Alby312/BalancerRobot_Mk1/Electronics/BalancerRobot_Mk1.kicad_sch

## KiCad design Electronics/BalancerRobot_Mk1.kicad_sch (2025-12-15)

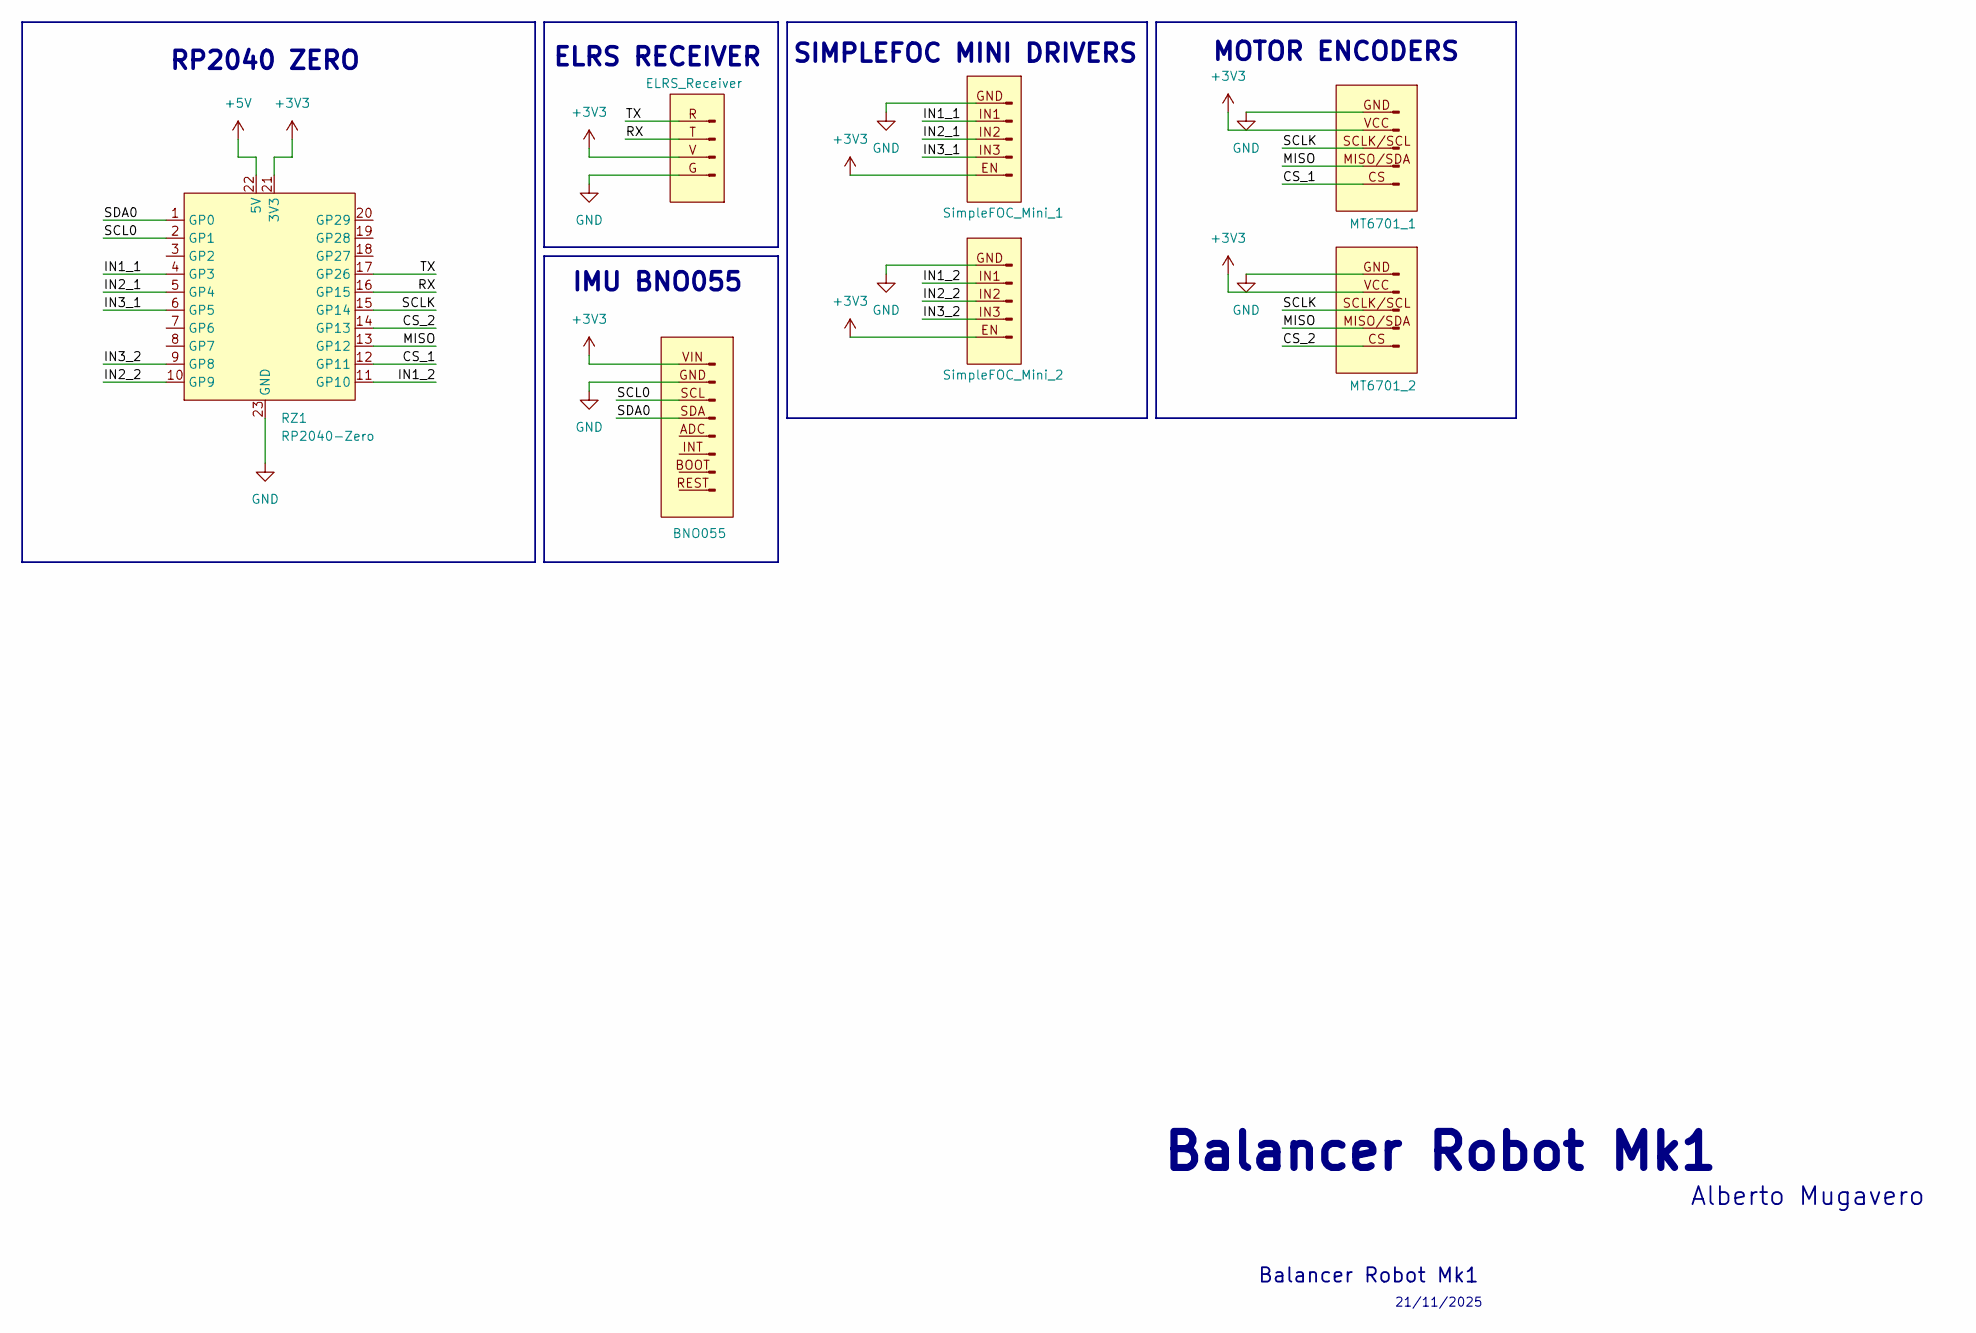
[picture p6: schematic BalancerRobot_Mk1.kicad_sch]

Parts:
BNO055: Conn_01x04_Pin
ELRS_Receiver: Conn_01x04_Pin
MT6701_1, MT6701_2: Conn_01x04_Pin
RZ1: RP2040-Zero
SimpleFOC_Mini_1, SimpleFOC_Mini_2: Conn_01x04_Pin

Connections:
+3V3: BNO055.VIN (Pin_1), ELRS_Receiver.V (Pin_2), MT6701_1.VCC (Pin_2), MT6701_2.VCC (Pin_2), RZ1.21 (3V3), SimpleFOC_Mini_1.EN (Pin_5), SimpleFOC_Mini_2.EN (Pin_5)
+5V: RZ1.22 (5V)
CS_1: MT6701_1.CS (Pin_5), RZ1.12 (GP11)
CS_2: MT6701_2.CS (Pin_5), RZ1.14 (GP13)
GND: BNO055.GND (Pin_2), ELRS_Receiver.G (Pin_1), MT6701_1.GND (Pin_1), MT6701_2.GND (Pin_1), RZ1.23 (GND), SimpleFOC_Mini_1.GND (Pin_1), SimpleFOC_Mini_2.GND (Pin_1)
IN1_1: RZ1.4 (GP3), SimpleFOC_Mini_1.IN1 (Pin_2)
IN1_2: RZ1.11 (GP10), SimpleFOC_Mini_2.IN1 (Pin_2)
IN2_1: RZ1.5 (GP4), SimpleFOC_Mini_1.IN2 (Pin_3)
IN2_2: RZ1.10 (GP9), SimpleFOC_Mini_2.IN2 (Pin_3)
IN3_1: RZ1.6 (GP5), SimpleFOC_Mini_1.IN3 (Pin_4)
IN3_2: RZ1.9 (GP8), SimpleFOC_Mini_2.IN3 (Pin_4)
MISO: MT6701_1.MISO/SDA (Pin_4), MT6701_2.MISO/SDA (Pin_4), RZ1.13 (GP12)
RX: ELRS_Receiver.T (Pin_3), RZ1.16 (GP15)
SCL0: BNO055.SCL (Pin_3), RZ1.2 (GP1)
SCLK: MT6701_1.SCLK/SCL (Pin_3), MT6701_2.SCLK/SCL (Pin_3), RZ1.15 (GP14)
SDA0: BNO055.SDA (Pin_4), RZ1.1 (GP0)
TX: ELRS_Receiver.R (Pin_4), RZ1.17 (GP26)

Notes on the sheet:
MOTOR ENCODERS
RP2040 ZERO
Alberto Mugavero
IMU BNO055
Balancer Robot Mk1
ELRS RECEIVER
SIMPLEFOC MINI DRIVERS
21/11/2025
